calvin-mcd/clops/Project/clops.kicad_sch

## KiCad design Project/clops.kicad_sch (2024-04-21)

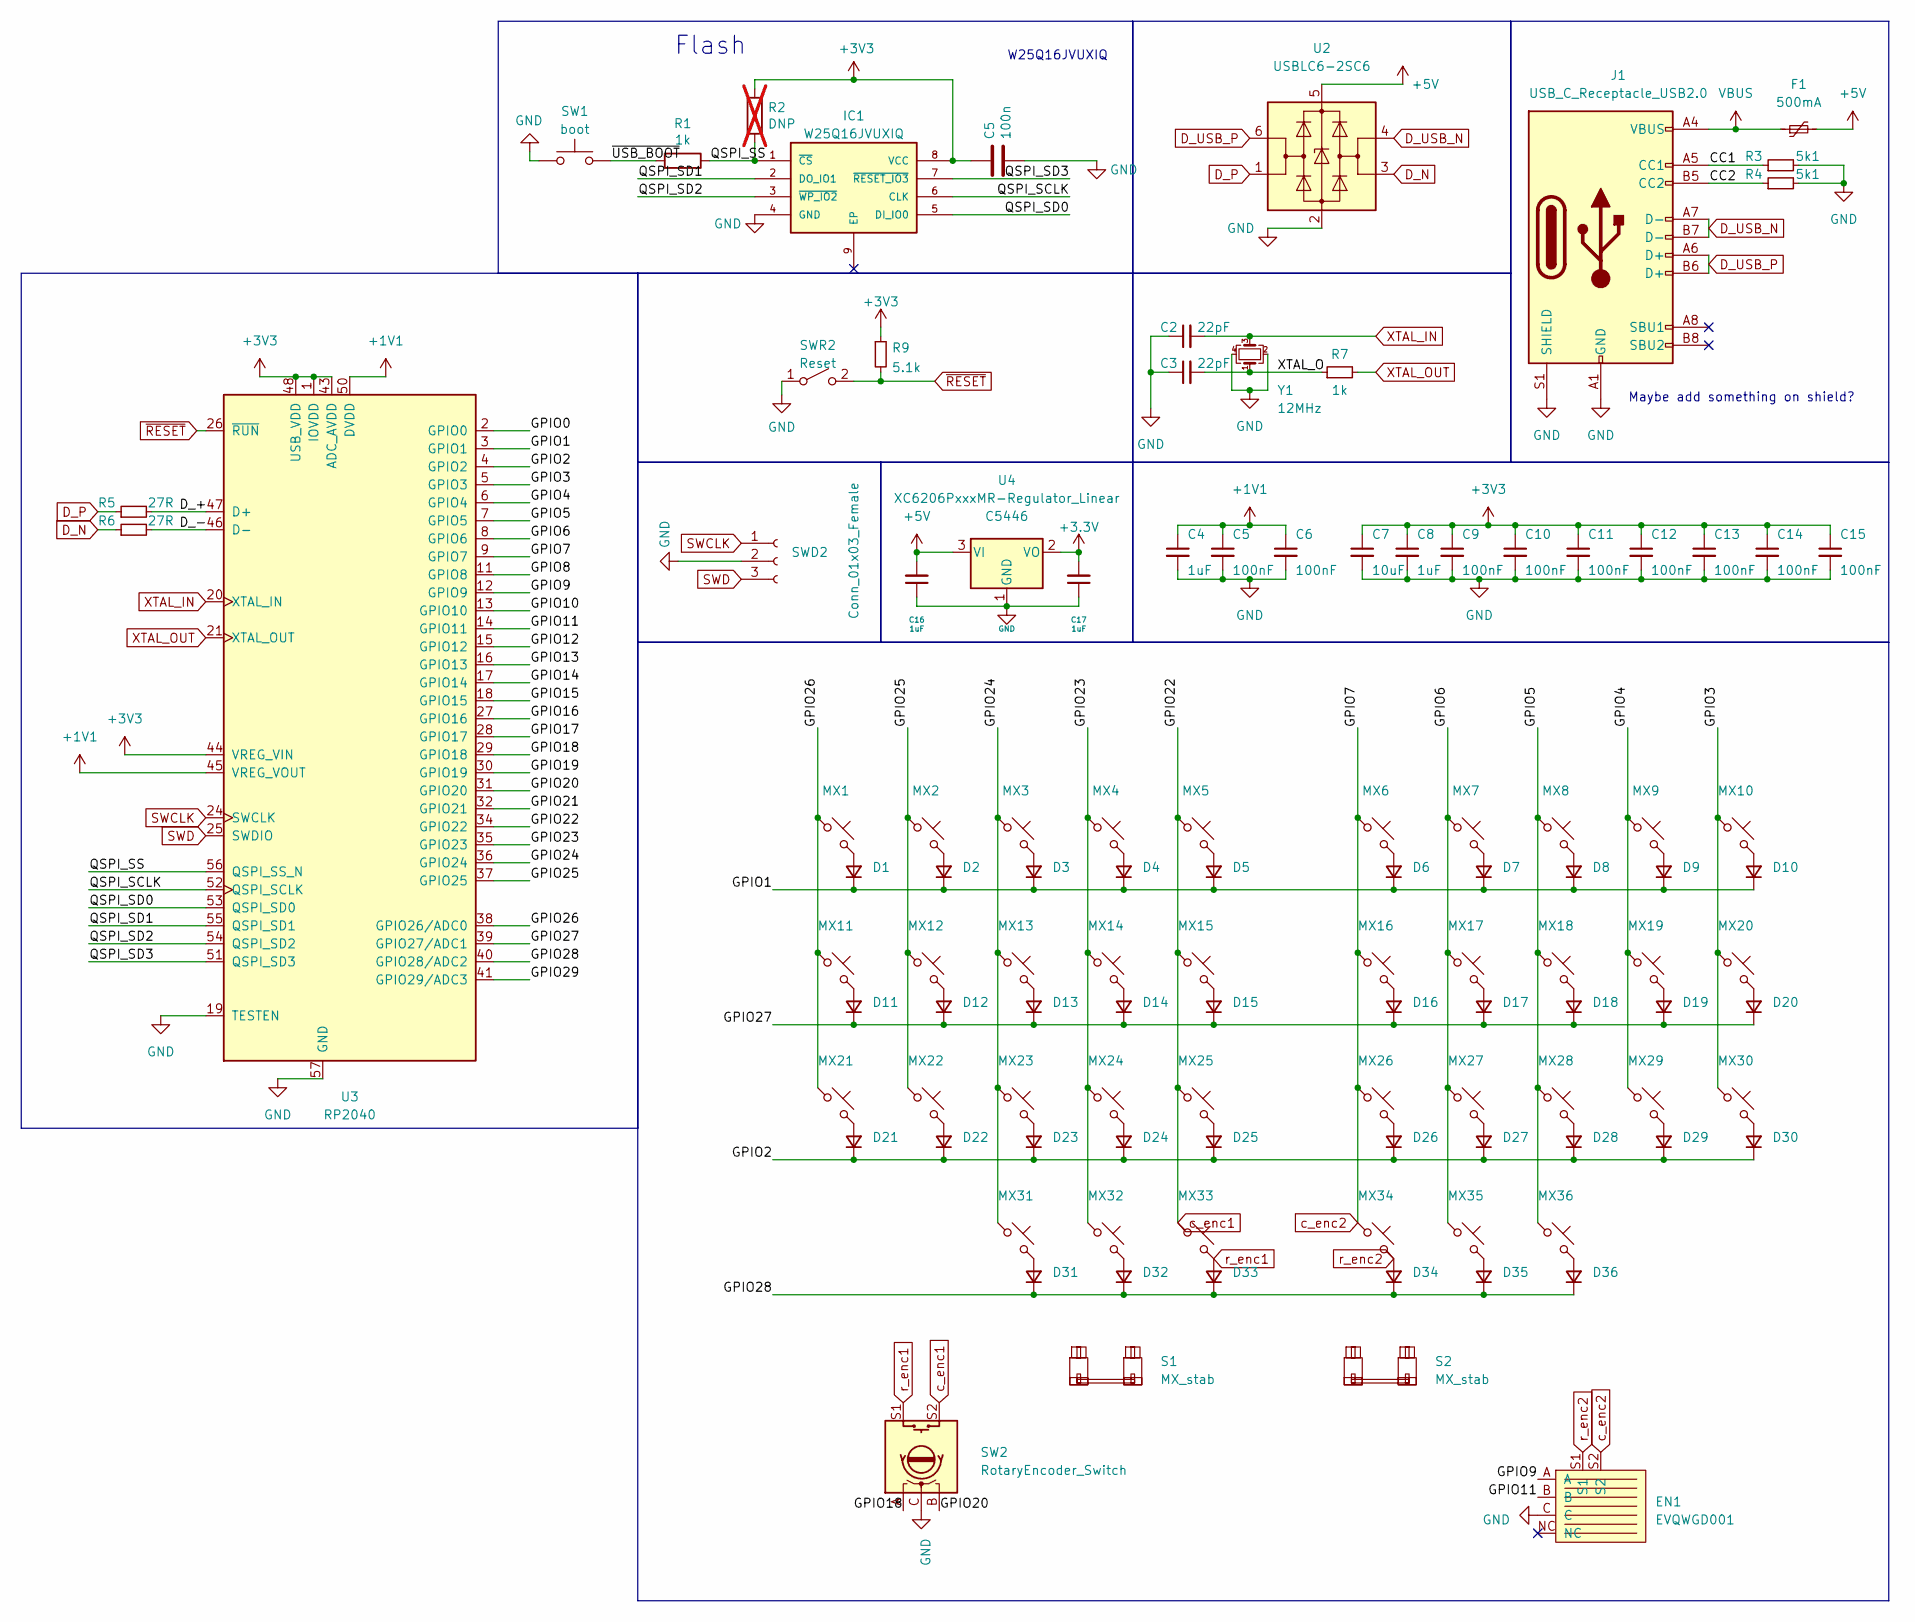
[picture p6: schematic clops.kicad_sch]

Parts:
C2, C3: 22pF; C_0402_1005Metric; LCSC C1555
C4, C8, C16, C17: 1uF; C_0402_1005Metric; LCSC C52923
C5: 100n; C_0402_1005Metric; LCSC C1525
C6, C9, C10, C11, C12, C13, C14, C15: 100nF; C_0402_1005Metric; LCSC C1525
C7: 10uF; C_0402_1005Metric; LCSC C15525
D1, D2, D3, D4, D5, D6, D7, D8, D9, D10, D11, D12, D13, D14, D15, D16, D17, D18, D19, D20, D21, D22, D23, D24, D25, D26, D27, D28, D29, D30, D31, D32, D33, D34, D35, D36: D_Small; D_SOD-123F
EN1: EVQWGD001; RollerEncoder
F1: 500mA; Fuse_1206_3216Metric; LCSC C70076
IC1: W25Q16JVUXIQ; SON50P300X200X60-9N; MANUFACTURER_PART_NUMBER W25Q16JVUXIQ; LCSC Part C2843335
J1: USB_C_Receptacle_USB2.0; USB_C_Receptacle_HRO_TYPE-C-31-M-12; LCSC C165948
MX1, MX10: MX_SW_HS; SW_MX_HS_CPG151101S11_1.5u
MX2, MX3, MX4, MX5, MX6, MX7, MX8, MX9, MX12, MX13, MX14, MX15, MX16, MX17, MX18, MX19, MX21, MX22, MX23, MX24, MX25, MX26, MX27, MX28, MX29, MX30, MX32, MX33, MX34, MX35: MX_SW_HS; SW_MX_HS_CPG151101S11_1u
MX11, MX20, MX31, MX36: MX_SW_HS; SW_MX_HS_CPG151101S11_1.25u
R1: 1k; R_0402_1005Metric; LCSC Part C25543
R2: DNP; C_0402_1005Metric; LCSC C25905; not fitted
R3, R4: 5k1; R_0402_1005Metric; LCSC C25905
R5, R6: 27R; R_0603_1608Metric; LCSC C25190
R7: 1k; R_0402_1005Metric; LCSC C11702
R9: 5.1k; R_0402_1005Metric
S1, S2: MX_stab; STAB_MX_P_2u
SW1: boot; SW_SPST_TL3342; LCSC Part C115351
SW2: RotaryEncoder_Switch; ROT_Alps_EC11E-Switch
SWD2: Conn_01x03_Female; PinHeader_1x03_P2.54mm_Vertical
SWR2: Reset; SW_SPST_TL3342
U2: USBLC6-2SC6; SOT-23-6; LCSC C2827654
U3: RP2040; RP2040-QFN-56; LCSC C2040
U4: XC6206PxxxMR-Regulator_Linear; SOT-23; LCSC C5446
Y1: 12MHz; Crystal_SMD_3225-4Pin_3.2x2.5mm; LCSC C9002

Connections:
+1V1: C4.1, C5.1, C6.1, U3.23 (DVDD), U3.45 (VREG_VOUT), U3.50 (DVDD)
+3.3V: C17.2, U4.2 (VO)
+3V3: C5.1, C7.1, C8.1, C9.1, C10.1, C11.1, C12.1, C13.1, C14.1, C15.1, IC1.8 (VCC), R2.1, R9.1, U3.1 (IOVDD), U3.10 (IOVDD), U3.22 (IOVDD), U3.33 (IOVDD), U3.42 (IOVDD), U3.43 (ADC_AVDD), U3.44 (VREG_VIN), U3.48 (USB_VDD), U3.49 (IOVDD)
+5V: C16.2, F1.2, U2.5 (VBUS), U4.3 (VI)
CC1: J1.A5 (CC1), R3.1
CC2: J1.B5 (CC2), R4.1
D_+: R5.2, U3.47 (D+)
D_-: R6.2, U3.46 (D-)
D_N: R6.1, U2.3 (I/O2)
D_P: R5.1, U2.1 (I/O1)
D_USB_N: J1.A7 (D-), J1.B7 (D-), U2.4 (I/O2)
D_USB_P: J1.A6 (D+), J1.B6 (D+), U2.6 (I/O1)
GND: C2.1, C3.1, C4.2, C5.2, C6.2, C7.2, C8.2, C9.2, C10.2, C11.2, C12.2, C13.2, C14.2, C15.2, C16.1, C17.1, EN1.C, IC1.4 (GND), J1.A1 (GND), J1.A12 (GND), J1.B1 (GND), J1.B12 (GND), J1.S1 (SHIELD), R3.2, R4.2, SW1.1, SW2.C, SWD2.2, SWR2.1 (A), U2.2 (GND), U3.19 (TESTEN), U3.57 (GND), U4.1 (GND), Y1.2, Y1.4
GPIO0: U3.2 (GPIO0)
GPIO1: D1.1 (K), D2.1 (K), D3.1 (K), D4.1 (K), D5.1 (K), D6.1 (K), D7.1 (K), D8.1 (K), D9.1 (K), D10.1 (K), U3.3 (GPIO1)
GPIO2: D21.1 (K), D22.1 (K), D23.1 (K), D24.1 (K), D25.1 (K), D26.1 (K), D27.1 (K), D28.1 (K), D29.1 (K), D30.1 (K), U3.4 (GPIO2)
GPIO3: MX10.1, MX20.1, MX30.1, U3.5 (GPIO3)
GPIO4: MX9.1, MX19.1, MX29.1, U3.6 (GPIO4)
GPIO5: MX8.1, MX18.1, MX28.1, MX36.1, U3.7 (GPIO5)
GPIO6: MX7.1, MX17.1, MX27.1, MX35.1, U3.8 (GPIO6)
GPIO8: U3.11 (GPIO8)
GPIO9: EN1.A, U3.12 (GPIO9)
GPIO10: U3.13 (GPIO10)
GPIO11: EN1.B, U3.14 (GPIO11)
GPIO12: U3.15 (GPIO12)
GPIO13: U3.16 (GPIO13)
GPIO14: U3.17 (GPIO14)
GPIO15: U3.18 (GPIO15)
GPIO16: U3.27 (GPIO16)
GPIO17: U3.28 (GPIO17)
GPIO18: SW2.A, U3.29 (GPIO18)
GPIO19: U3.30 (GPIO19)
GPIO20: SW2.B, U3.31 (GPIO20)
GPIO21: U3.32 (GPIO21)
GPIO23: MX4.1, MX14.1, MX24.1, MX32.1, U3.35 (GPIO23)
GPIO24: MX3.1, MX13.1, MX23.1, MX31.1, U3.36 (GPIO24)
GPIO25: MX2.1, MX12.1, MX22.1, U3.37 (GPIO25)
GPIO26: MX1.1, MX11.1, MX21.1, U3.38 (GPIO26/ADC0)
GPIO27: D11.1 (K), D12.1 (K), D13.1 (K), D14.1 (K), D15.1 (K), D16.1 (K), D17.1 (K), D18.1 (K), D19.1 (K), D20.1 (K), U3.39 (GPIO27/ADC1)
GPIO28: D31.1 (K), D32.1 (K), D33.1 (K), D34.1 (K), D35.1 (K), D36.1 (K), U3.40 (GPIO28/ADC2)
GPIO29: U3.41 (GPIO29/ADC3)
unnamed: D1.2 (A), MX1.2
unnamed: D2.2 (A), MX2.2
unnamed: D3.2 (A), MX3.2
unnamed: D4.2 (A), MX4.2
unnamed: D5.2 (A), MX5.2
unnamed: D6.2 (A), MX6.2
unnamed: D7.2 (A), MX7.2
unnamed: D8.2 (A), MX8.2
unnamed: D9.2 (A), MX9.2
unnamed: D10.2 (A), MX10.2
unnamed: D11.2 (A), MX11.2
unnamed: D12.2 (A), MX12.2
unnamed: D13.2 (A), MX13.2
unnamed: D14.2 (A), MX14.2
unnamed: D15.2 (A), MX15.2
unnamed: D16.2 (A), MX16.2
unnamed: D17.2 (A), MX17.2
unnamed: D18.2 (A), MX18.2
unnamed: D19.2 (A), MX19.2
unnamed: D20.2 (A), MX20.2
unnamed: D21.2 (A), MX21.2
unnamed: D22.2 (A), MX22.2
unnamed: D23.2 (A), MX23.2
unnamed: D24.2 (A), MX24.2
unnamed: D25.2 (A), MX25.2
unnamed: D26.2 (A), MX26.2
unnamed: D27.2 (A), MX27.2
unnamed: D28.2 (A), MX28.2
unnamed: D29.2 (A), MX29.2
unnamed: D30.2 (A), MX30.2
unnamed: D31.2 (A), MX31.2
unnamed: D32.2 (A), MX32.2
unnamed: D35.2 (A), MX35.2
unnamed: D36.2 (A), MX36.2
QSPI_SCLK: IC1.6 (CLK), U3.52 (QSPI_SCLK)
QSPI_SD0: IC1.5 (DI_IO0), U3.53 (QSPI_SD0)
QSPI_SD1: IC1.2 (DO_IO1), U3.55 (QSPI_SD1)
QSPI_SD2: IC1.3 (~WP_IO2), U3.54 (QSPI_SD2)
QSPI_SD3: IC1.7 (~RESET_IO3), U3.51 (QSPI_SD3)
QSPI_SS: IC1.1 (~CS), R1.1, R2.2, U3.56 (QSPI_SS_N)
SWCLK: SWD2.1, U3.24 (SWCLK)
SWD: SWD2.3, U3.25 (SWDIO)
VBUS: F1.1, J1.A4 (VBUS), J1.A9 (VBUS), J1.B4 (VBUS), J1.B9 (VBUS)
XTAL_IN: C2.2, U3.20 (XTAL_IN), Y1.3
XTAL_O: C3.2, R7.1, Y1.1
XTAL_OUT: R7.2, U3.21 (XTAL_OUT)
c_enc1: MX5.1, MX15.1, MX25.1, MX33.1, SW2.S2, U3.34 (GPIO22)
c_enc2: EN1.S2, MX6.1, MX16.1, MX26.1, MX34.1, U3.9 (GPIO7)
r_enc1: D33.2 (A), MX33.2, SW2.S1
r_enc2: D34.2 (A), EN1.S1, MX34.2
~RESET: R9.2, SWR2.2 (B), U3.26 (~RUN)
~USB_BOOT: R1.2, SW1.2

Notes on the sheet:
Flash
W25Q16JVUXIQ
Maybe add something on shield?
