calvin-mcd/clops/Firmware/Source Code/keymaps/vial/config.h

#define VIAL_KEYBOARD_UID {0xA1, 0x6E, 0xF2, 0x02, 0x8D, 0xBE, 0x7F, 0x33}

#define VIAL_UNLOCK_COMBO_ROWS { 0, 0 }
#define VIAL_UNLOCK_COMBO_COLS { 0, 1 }

#define VIAL_TAP_DANCE_ENTRIES 16
#define VIAL_COMBO_ENTRIES 69

#define DYNAMIC_KEYMAP_LAYER_COUNT 16
